andres-garcia-alves/electronic-luminous-touch-toy/Resources/22-box-shaping-01.jpg

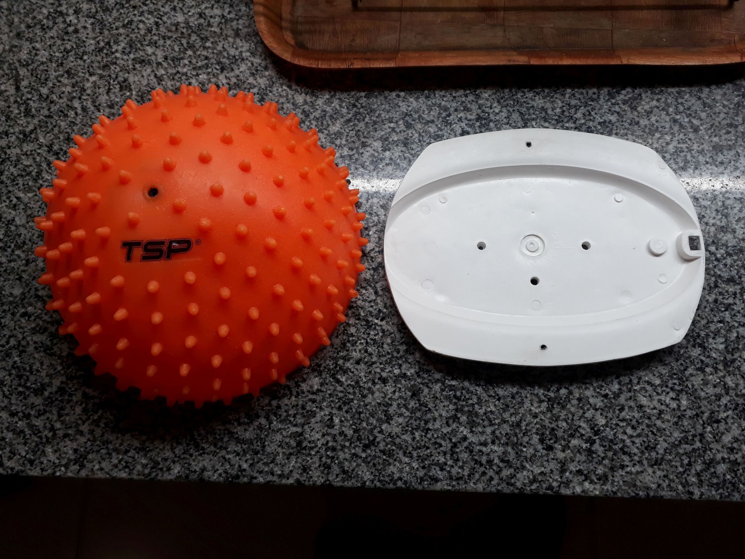
Resources/22-box-shaping-01.jpg
