andres-garcia-alves/electronic-luminous-touch-toy/Resources/23-box-shaping-02.jpg

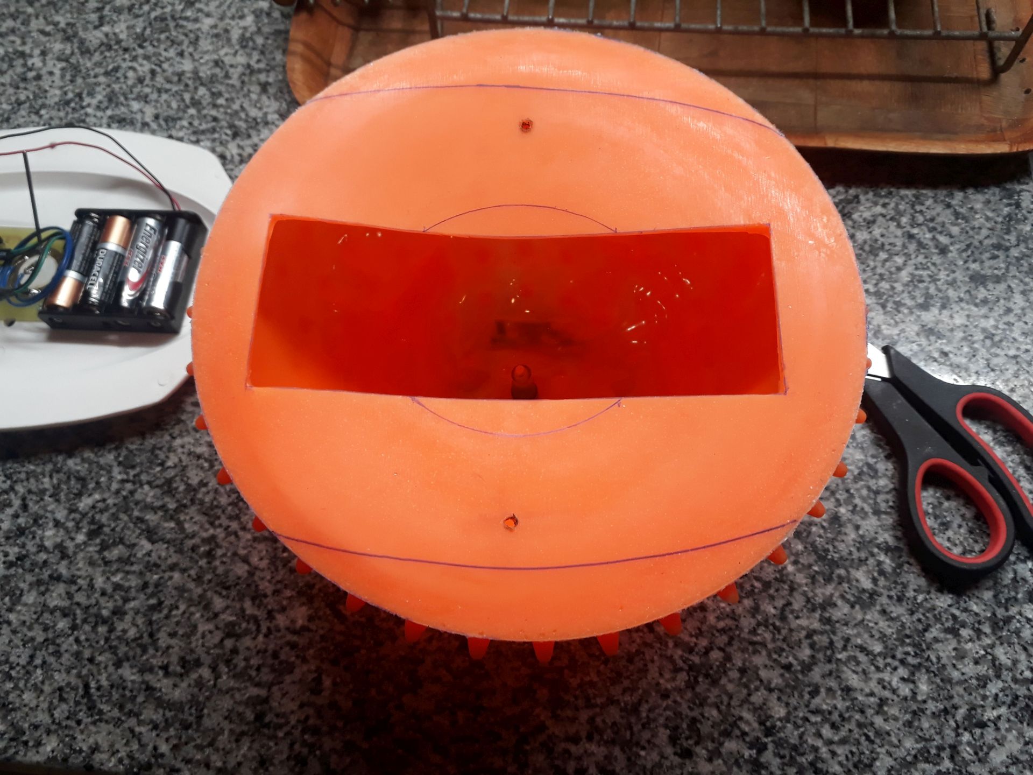
Resources/23-box-shaping-02.jpg
