andres-garcia-alves/electronic-luminous-touch-toy/Resources/10-pcb-manufacturing-03.jpg

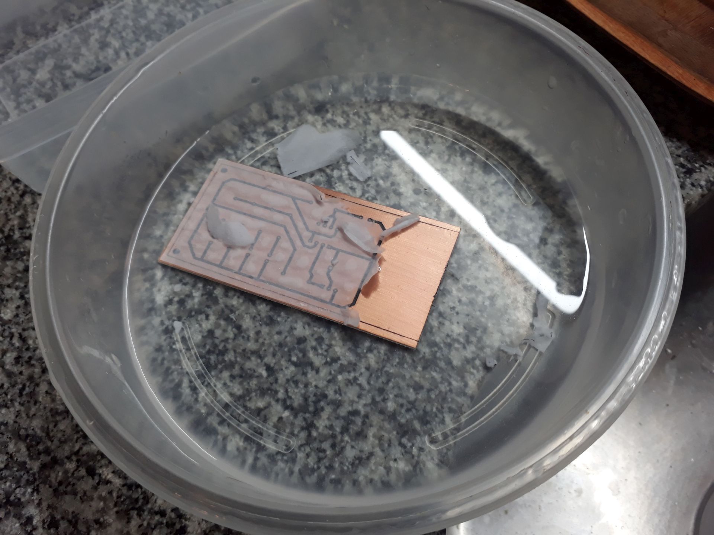
Resources/10-pcb-manufacturing-03.jpg
