andres-garcia-alves/electronic-luminous-touch-toy/Resources/11-pcb-manufacturing-04.jpg

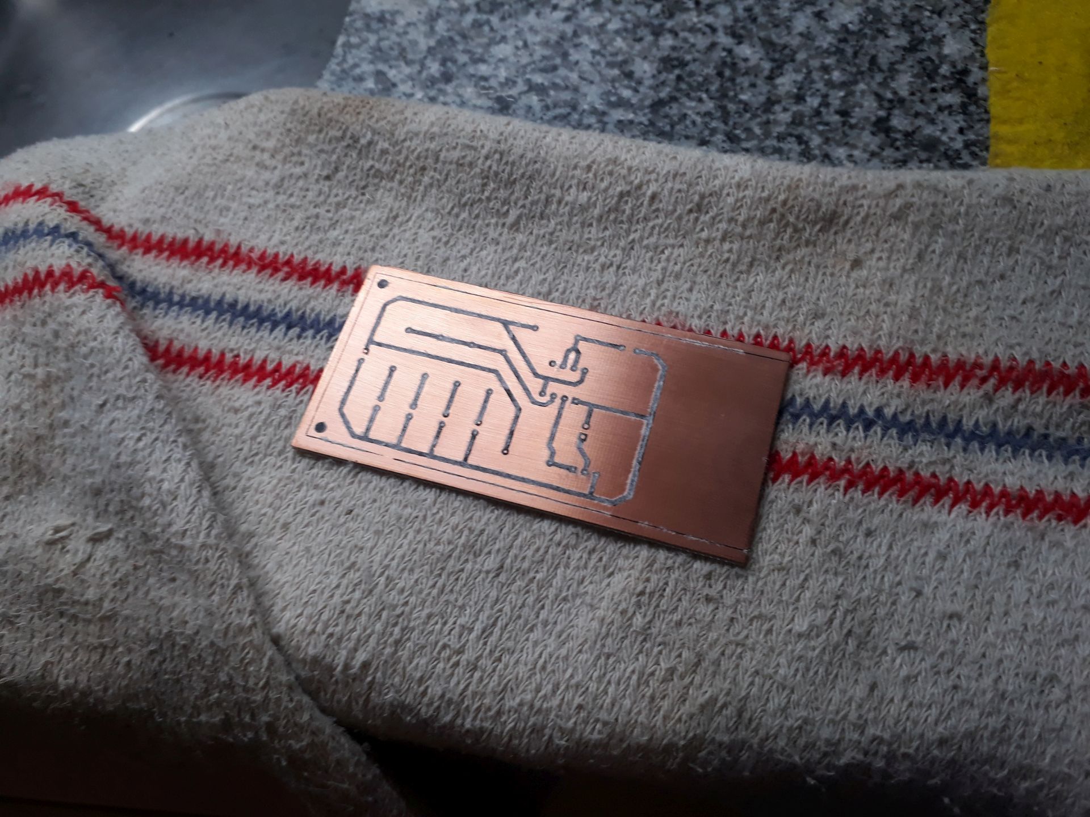
Resources/11-pcb-manufacturing-04.jpg
