andres-garcia-alves/electronic-luminous-touch-toy/Resources/12-pcb-manufacturing-05.jpg

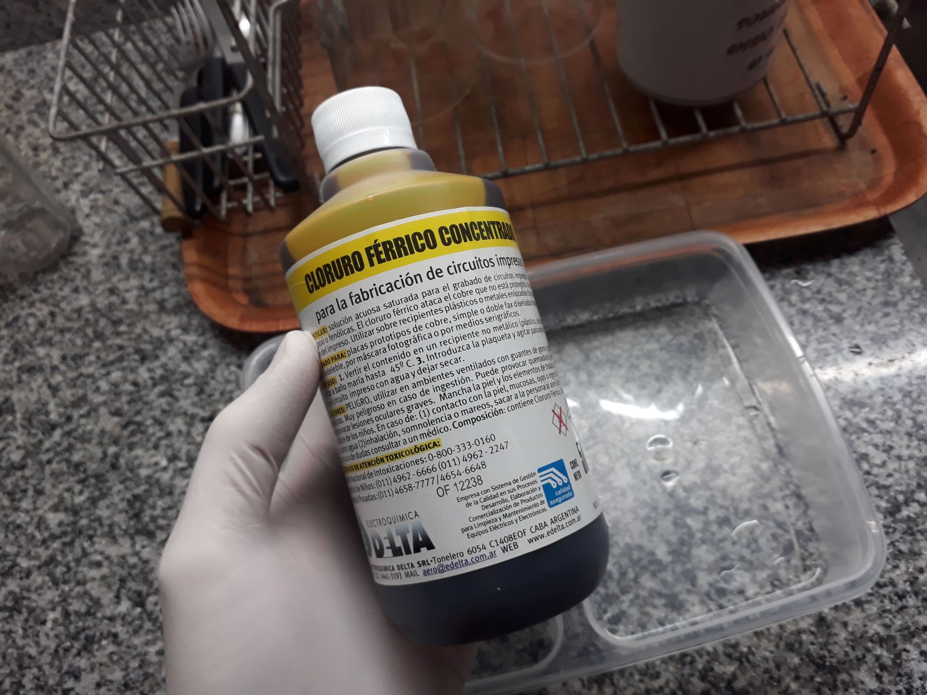
Resources/12-pcb-manufacturing-05.jpg
