andres-garcia-alves/electronic-luminous-touch-toy/Resources/13-pcb-manufacturing-06.jpg

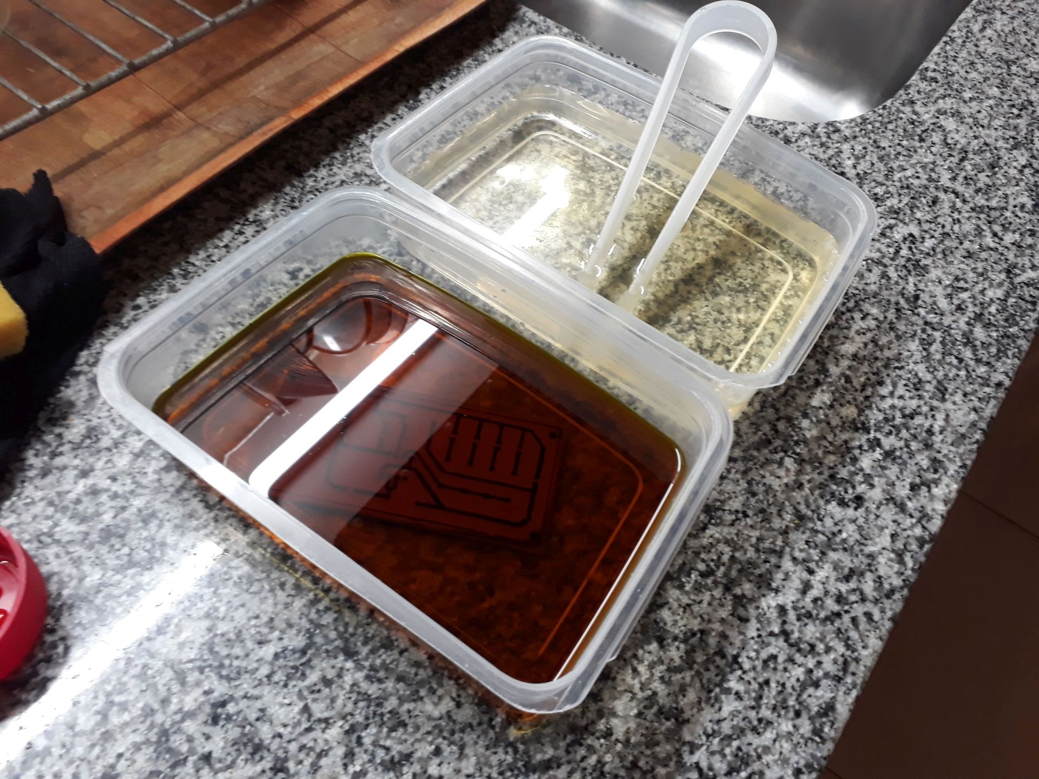
Resources/13-pcb-manufacturing-06.jpg
