andres-garcia-alves/electronic-luminous-touch-toy/Resources/20-pcb-assembly-02.jpg

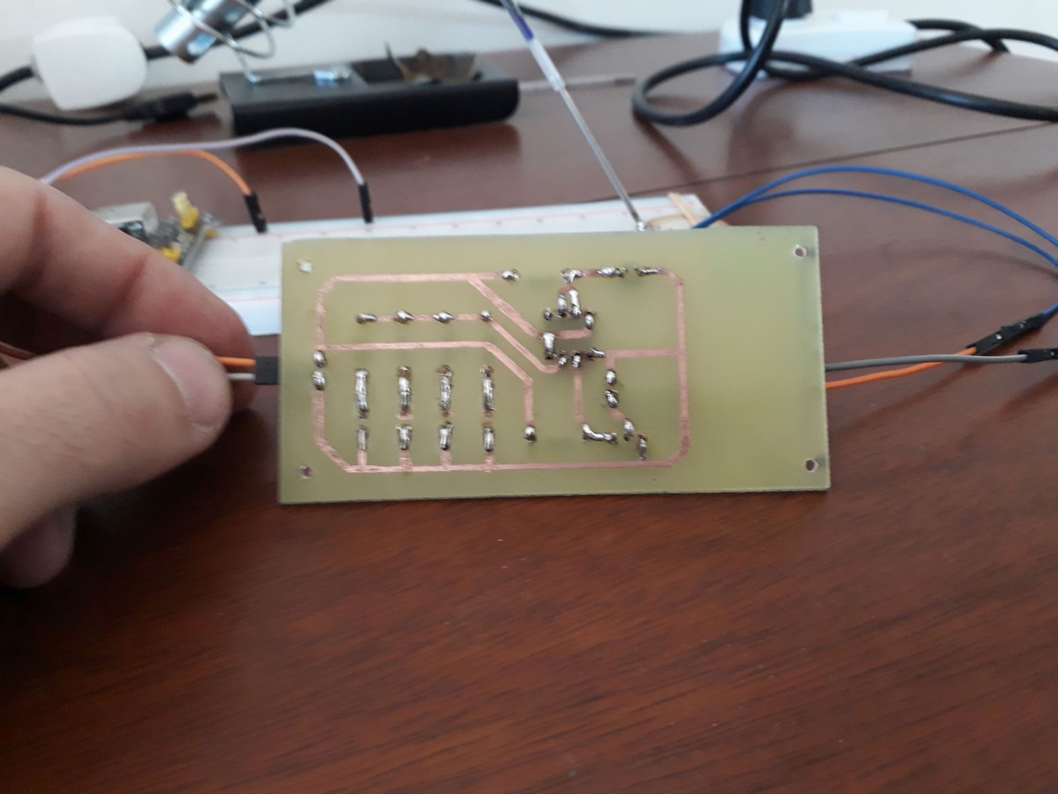
Resources/20-pcb-assembly-02.jpg
